Luk9091/Inzynierka/Documentation/Img/PathFinding/Dikstra_pathFinding_sharpTurn.png

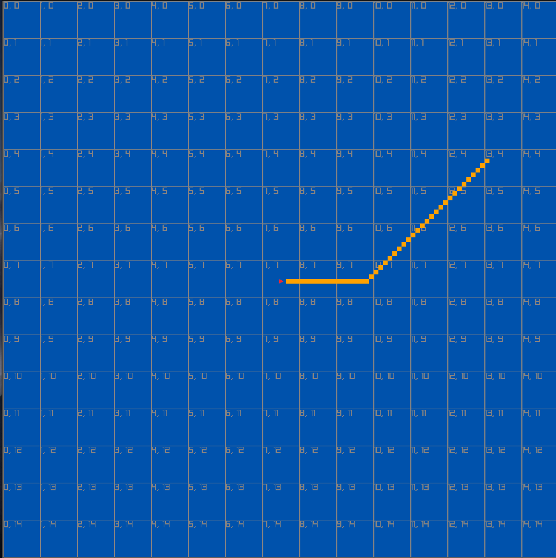
Documentation/Img/PathFinding/Dikstra_pathFinding_sharpTurn.png
