Luk9091/Inzynierka/Documentation/Img/Terminial.png

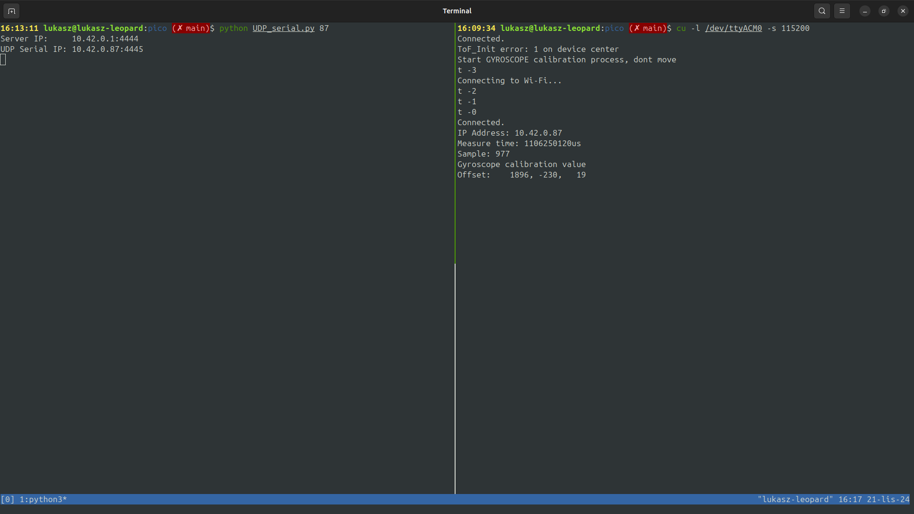
Documentation/Img/Terminial.png
