Luk9091/Inzynierka/Documentation/Measure/distance_no_PID_speed_50.csv

Time | Left | Right | Diff
0.0 | 0.0 | 0.0 | 0.0
0.1 | 11.525 | 20.549 | -9.024
0.2 | 36.967 | 59.581 | -22.615
0.3 | 67.41 | 101.876 | -34.466
0.4 | 100.68 | 140.256 | -39.576
0.501 | 135.037 | 185.159 | -50.122
0.601 | 171.786 | 225.388 | -53.602
0.701 | 208.535 | 261.811 | -53.275
0.801 | 244.849 | 295.407 | -50.557
0.901 | 279.207 | 333.352 | -54.145
1.001 | 313.129 | 365.208 | -52.079
1.101 | 351.618 | 397.174 | -45.556
1.201 | 389.78 | 429.574 | -39.793
1.301 | 429.574 | 463.931 | -34.357
1.402 | 467.628 | 497.853 | -30.226
1.502 | 503.942 | 530.906 | -26.964
1.602 | 540.039 | 563.306 | -23.267
1.702 | 575.375 | 595.38 | -20.005
1.802 | 615.385 | 627.671 | -12.286
1.902 | 656.375 | 659.854 | -3.479
2.002 | 697.691 | 692.037 | 5.654
2.102 | 736.832 | 726.394 | 10.438
2.202 | 771.406 | 760.208 | 11.199
2.303 | 808.59 | 793.804 | 14.787
2.403 | 847.405 | 826.965 | 20.44
2.503 | 881.219 | 860.235 | 20.984
2.603 | 915.033 | 893.396 | 21.636
2.703 | 949.607 | 927.862 | 21.745
2.803 | 989.944 | 961.241 | 28.703
2.903 | 1028.107 | 997.664 | 30.443
3.003 | 1065.4 | 1032.13 | 33.27
3.103 | 1099.974 | 1064.312 | 35.662
3.204 | 1135.419 | 1097.909 | 37.51
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
