Luk9091/Inzynierka/Documentation/Measure/speed.csv

duty | speedL | speedR
10 | 35.20 | 35.12
20 | 108.78 | 108.63
30 | 166.10 | 165.90
40 | 180.93 | 180.84
50 | 181.05 | 181.18
60 | 181.92 | 182.19
70 | 182.96 | 183.39
